OfficeChromatography/oclab2/Construction Set/Y_moving/STL/tower_distance_check.stl

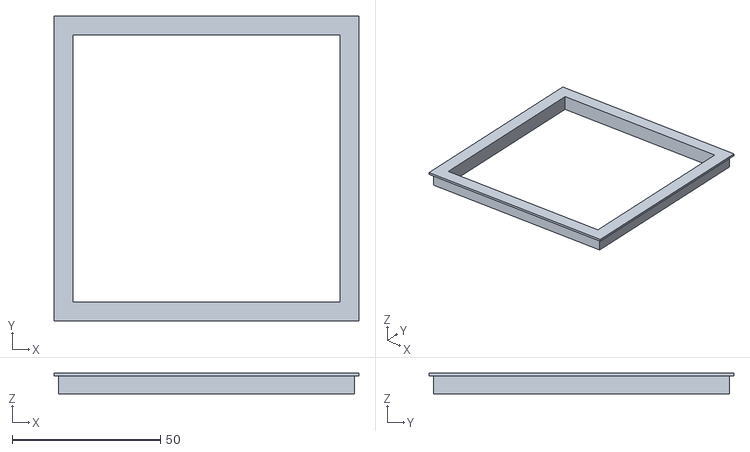
[picture p16: CAD file, 2021-02-09]
Construction Set/Y_moving/STL/tower_distance_check.stl
103.0 x 103.0 x 7.00
