OfficeChromatography/oclab2/Construction Set/camera_tower/STL/mounting_frame.stl

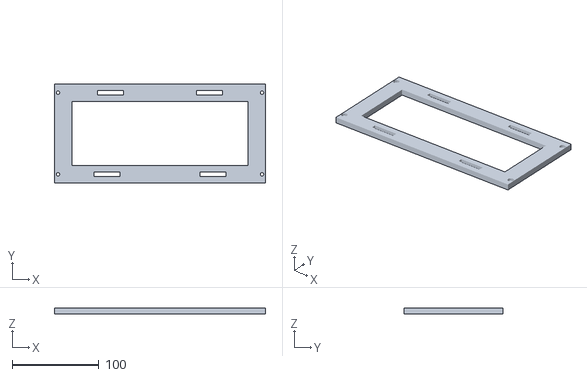
[picture p17: CAD file, 2021-02-09]
Construction Set/camera_tower/STL/mounting_frame.stl
243.0 x 114.0 x 7.00
