OfficeChromatography/oclab2/Construction Set/faces_frames/STL/back_top.stl

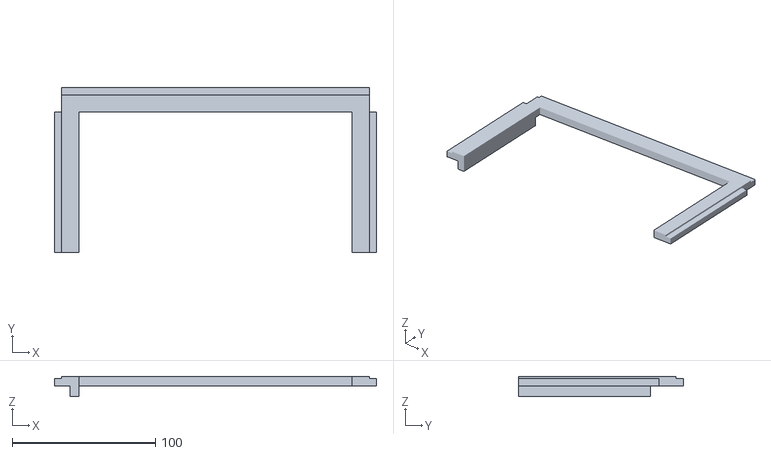
[picture p18: CAD file, 2021-02-09]
Construction Set/faces_frames/STL/back_top.stl
225.0 x 115.0 x 14.0
