OfficeChromatography/oclab2/Construction Set/X_moving/STL/X_moving.stl

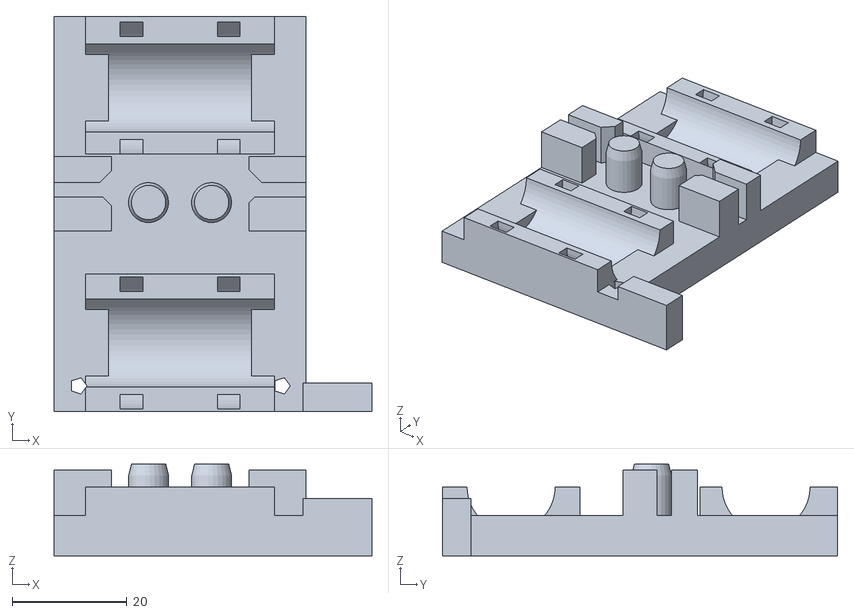
[picture p19: CAD file, 2021-02-09]
Construction Set/X_moving/STL/X_moving.stl
55.5 x 69.0 x 16.0
