OfficeChromatography/oclab2/Construction Set/Y_moving/STL/Y_motor.stl

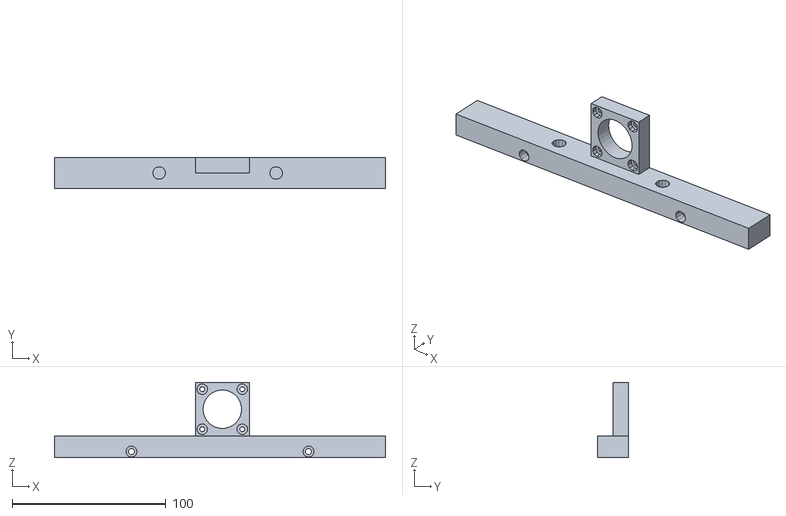
[picture p20: CAD file, 2021-02-09]
Construction Set/Y_moving/STL/Y_motor.stl
215.0 x 20.0 x 49.0
