OfficeChromatography/oclab2/Construction Set/faces_frames/STL/back_frames.stl

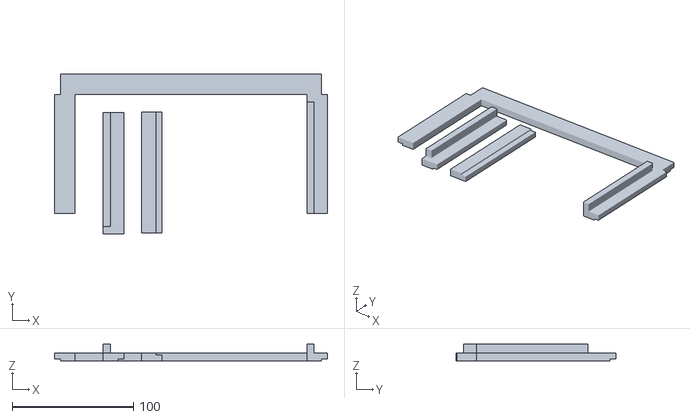
[picture p21: CAD file, 2021-02-09]
Construction Set/faces_frames/STL/back_frames.stl
225.0 x 131.9 x 14.0
