OfficeChromatography/oclab2/Construction Set/Y_moving/STL/plateholder_heating_mat.stl

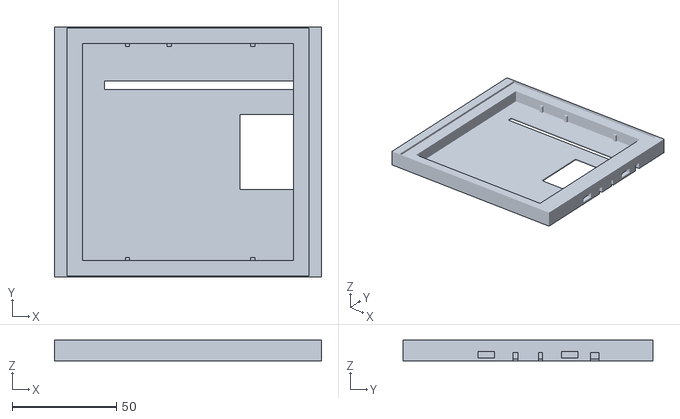
[picture p22: CAD file, 2021-02-09]
Construction Set/Y_moving/STL/plateholder_heating_mat.stl
128.0 x 120.0 x 10.0
