OfficeChromatography/oclab2/Construction Set/faces_frames/STL/right_front.stl

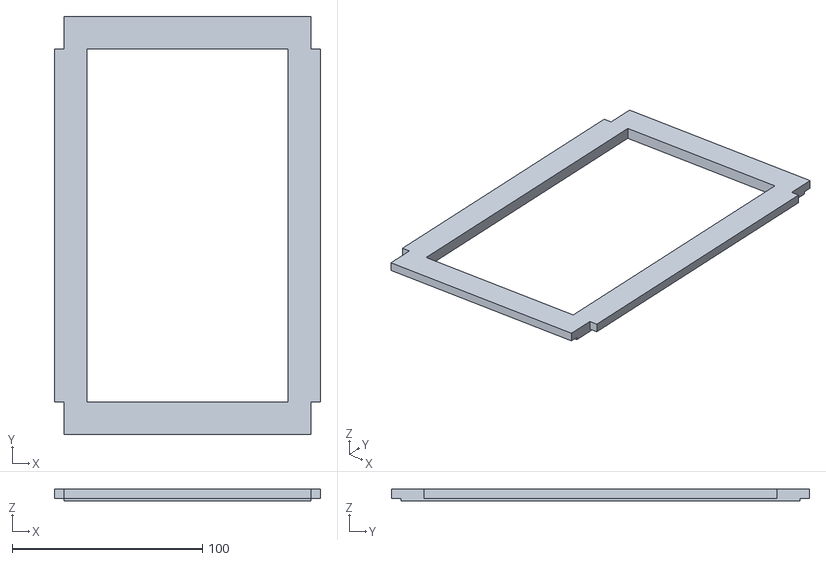
[picture p23: CAD file, 2021-02-09]
Construction Set/faces_frames/STL/right_front.stl
140.0 x 220.0 x 6.50
