OfficeChromatography/oclab2/Construction Set/X_moving/STL/printhead_bottom.stl

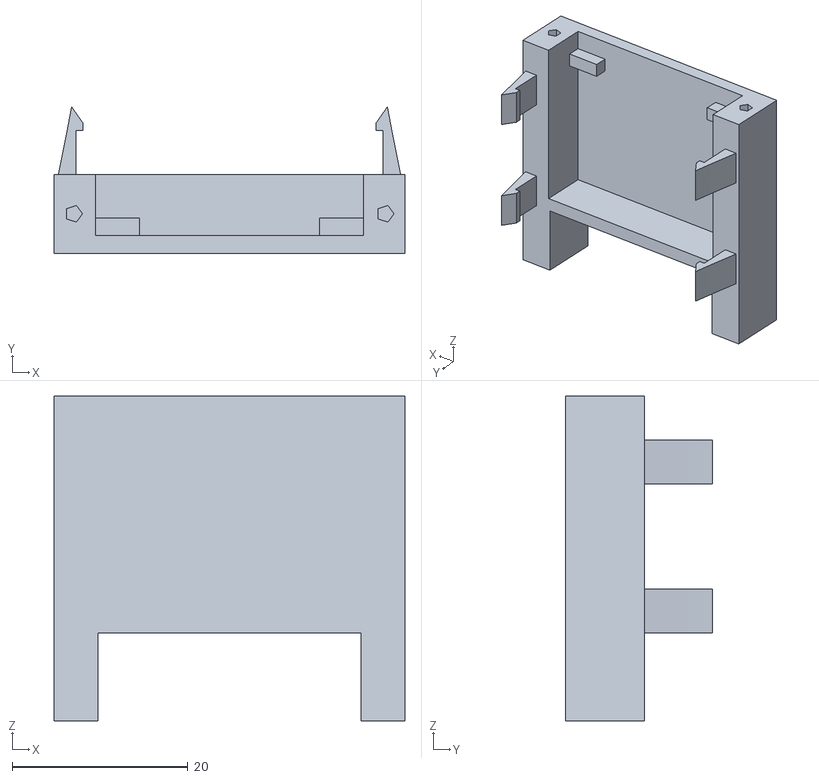
[picture p24: CAD file, 2021-02-09]
Construction Set/X_moving/STL/printhead_bottom.stl
40.0 x 16.7 x 37.0
