OfficeChromatography/oclab2/Construction Set/Y_moving/STL/Y_end.stl

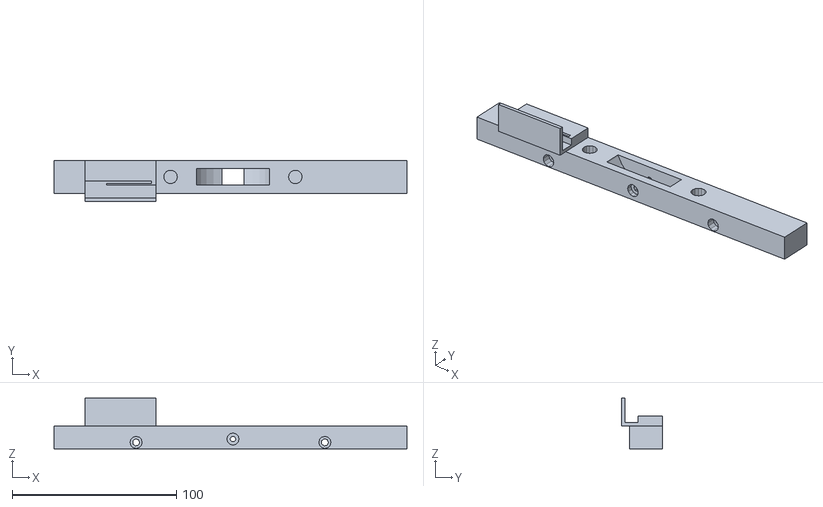
[picture p25: CAD file, 2021-02-09]
Construction Set/Y_moving/STL/Y_end.stl
215.0 x 25.0 x 31.0
