OfficeChromatography/oclab2/Construction Set/faces_frames/STL/bottom_front.stl

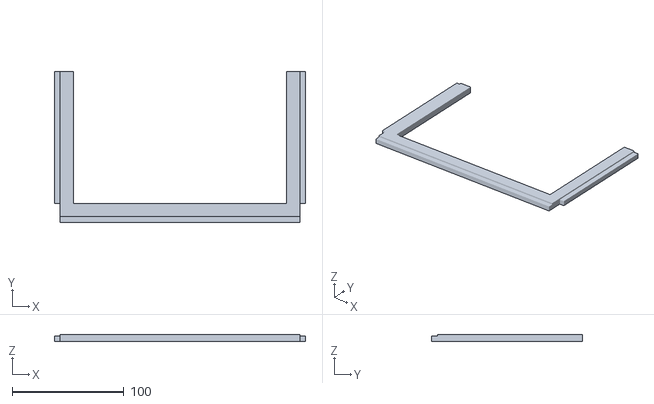
[picture p26: CAD file, 2021-02-09]
Construction Set/faces_frames/STL/bottom_front.stl
225.0 x 135.0 x 6.50
