OfficeChromatography/oclab2/Construction Set/Y_moving/STL/plateholder.stl

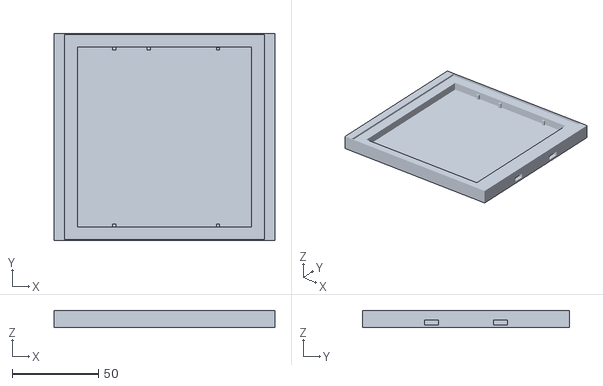
[picture p27: CAD file, 2021-02-09]
Construction Set/Y_moving/STL/plateholder.stl
128.0 x 120.0 x 10.0
