OfficeChromatography/oclab2/Construction Set/faces_frames/STL/lettering.stl

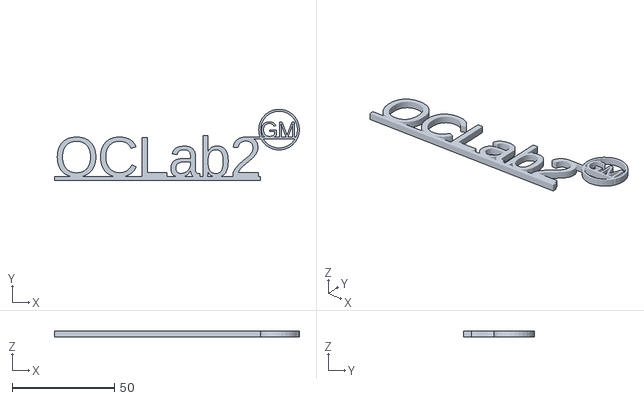
[picture p28: CAD file, 2021-02-09]
Construction Set/faces_frames/STL/lettering.stl
120.0 x 34.9 x 3.00
