OfficeChromatography/oclab2/Construction Set/X_moving/STL/X_motor.stl

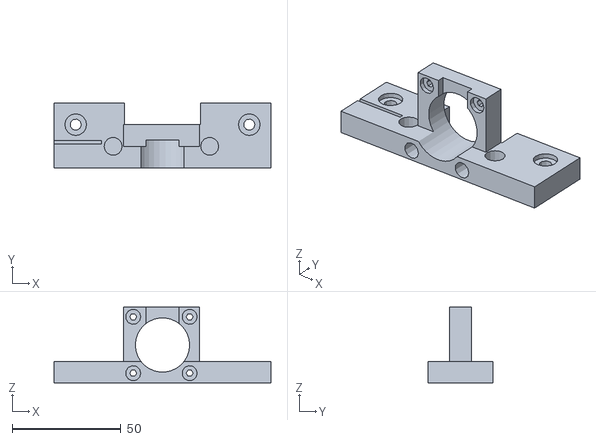
[picture p29: CAD file, 2021-02-09]
Construction Set/X_moving/STL/X_motor.stl
100.0 x 30.0 x 35.0
