OfficeChromatography/oclab2/Construction Set/Y_moving/STL/plateholder_plate_tower_frame.stl

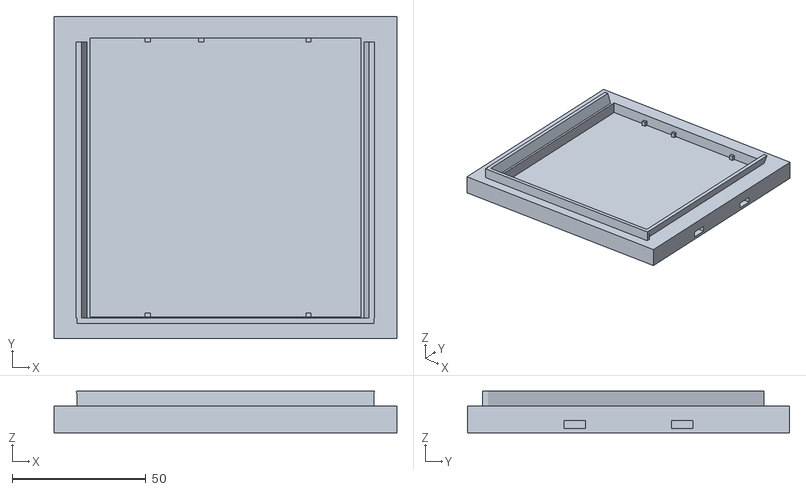
[picture p30: CAD file, 2021-02-09]
Construction Set/Y_moving/STL/plateholder_plate_tower_frame.stl
128.0 x 120.0 x 15.5
