OfficeChromatography/oclab2/Construction Set/faces_frames/STL/sides_back.stl

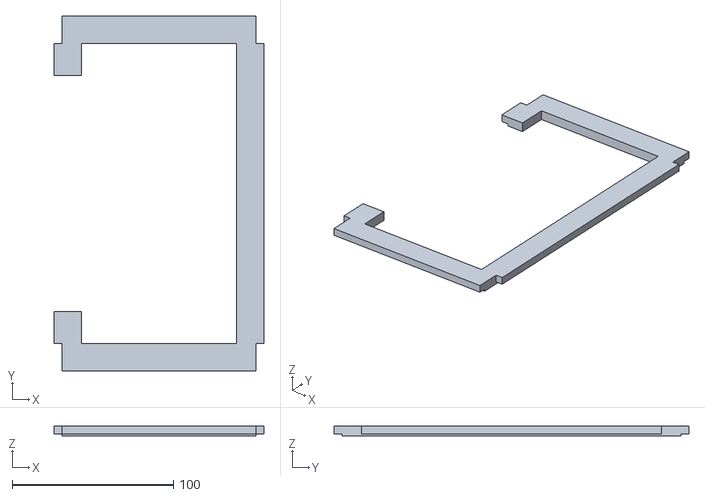
[picture p31: CAD file, 2021-02-09]
Construction Set/faces_frames/STL/sides_back.stl
130.0 x 220.0 x 6.50
