OfficeChromatography/oclab2/Construction Set/X_moving/STL/X_moving-2.stl

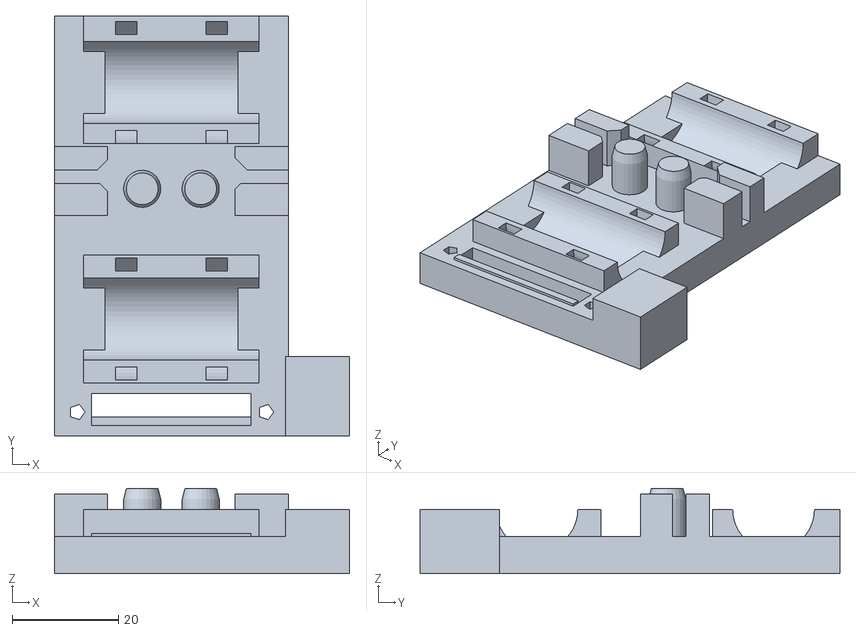
[picture p32: CAD file, 2021-02-09]
Construction Set/X_moving/STL/X_moving-2.stl
55.5 x 79.0 x 16.0
