OfficeChromatography/oclab2/Construction Set/faces_frames/STL/left_front_cable_channel.stl

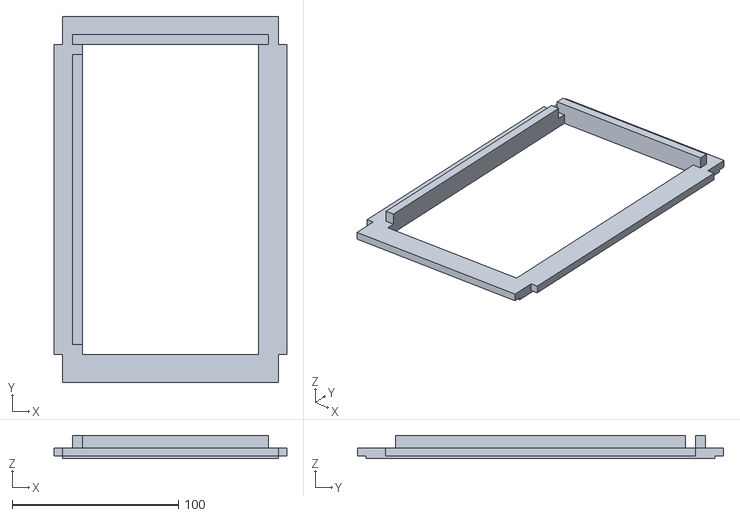
[picture p33: CAD file, 2021-02-09]
Construction Set/faces_frames/STL/left_front_cable_channel.stl
140.0 x 220.0 x 14.0
