OfficeChromatography/oclab2/Construction Set/faces_frames/STL/bottom_plate_front.stl

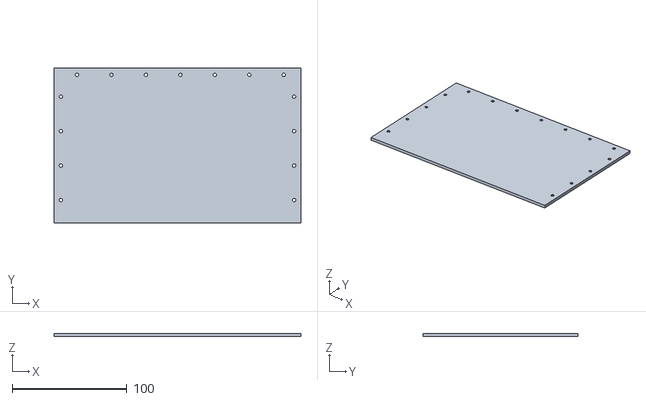
[picture p34: CAD file, 2021-02-09]
Construction Set/faces_frames/STL/bottom_plate_front.stl
215.0 x 135.0 x 3.00
