OfficeChromatography/oclab2/Construction Set/faces_frames/STL/back_bottom.stl

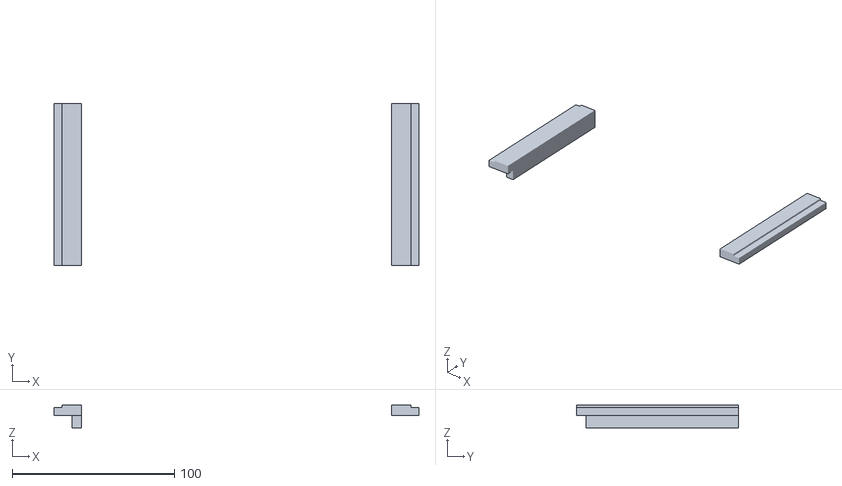
[picture p35: CAD file, 2021-02-09]
Construction Set/faces_frames/STL/back_bottom.stl
225.0 x 100.0 x 14.0
