OfficeChromatography/oclab2/Construction Set/faces_frames/STL/drilling_jig.stl

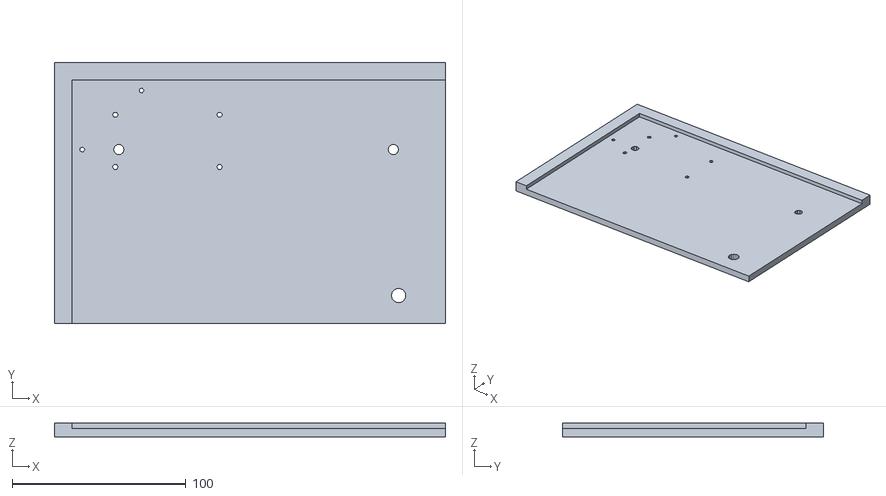
[picture p36: CAD file, 2021-02-09]
Construction Set/faces_frames/STL/drilling_jig.stl
225.0 x 150.0 x 8.00
