OfficeChromatography/oclab2/Construction Set/faces_frames/STL/bottom_back.stl

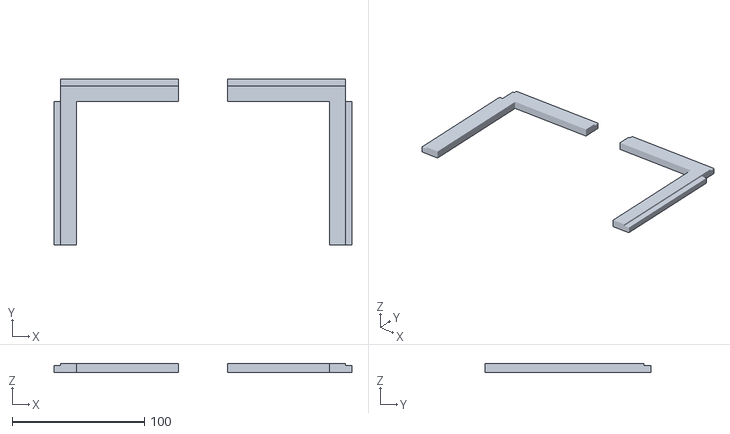
[picture p37: CAD file, 2021-02-09]
Construction Set/faces_frames/STL/bottom_back.stl
225.0 x 125.0 x 6.50
