OfficeChromatography/oclab2/Construction Set/faces_frames/STL/cover_top.stl

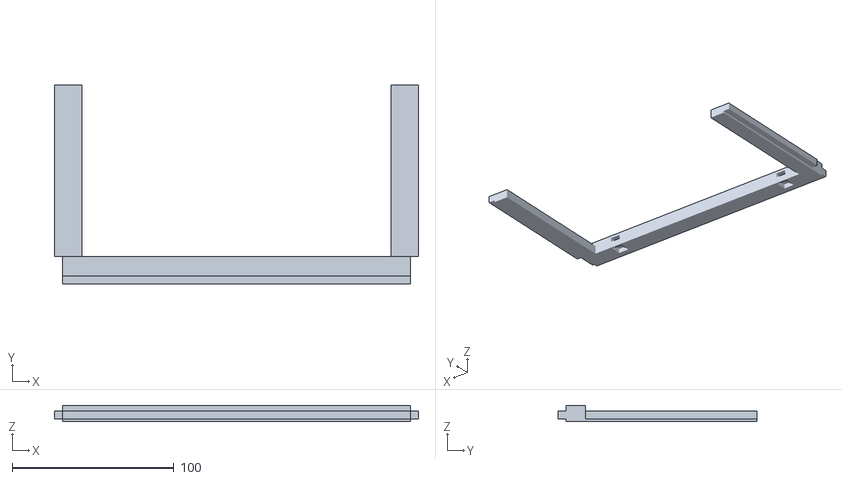
[picture p38: CAD file, 2021-02-09]
Construction Set/faces_frames/STL/cover_top.stl
225.0 x 123.0 x 10.0
