OfficeChromatography/oclab2/Construction Set/camera_tower/SCAD/cutting_aid_HU02_filter.scad

//cutting aid for HU 02 glass filter

difference() {
 cube([100, 50, 6]);
 translate([25, 27, 3]) cube([51, 50, 3]);    
}
